afteraincc/Simple-AR/3d-model/debug/lens-2.step

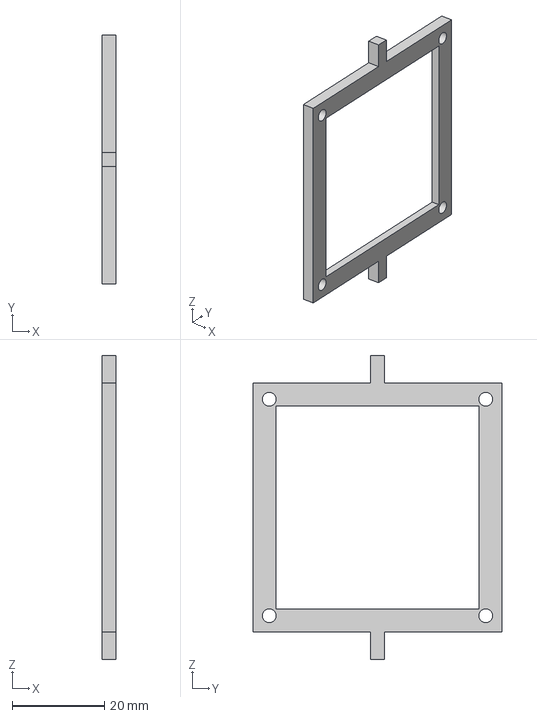
[picture p23: CAD file, 2023-01-13]
3d-model/debug/lens-2.step
3.00 x 54.0 x 66.0 mm
