afteraincc/Simple-AR/3d-model/debug/back.step

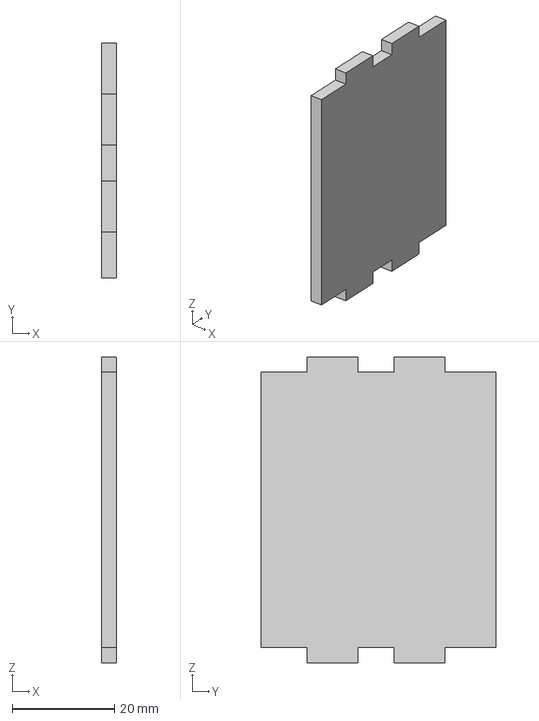
[picture p24: CAD file, 2023-01-13]
3d-model/debug/back.step
3.00 x 46.0 x 59.9 mm
