afteraincc/Simple-AR/3d-model/debug/beam-top.step

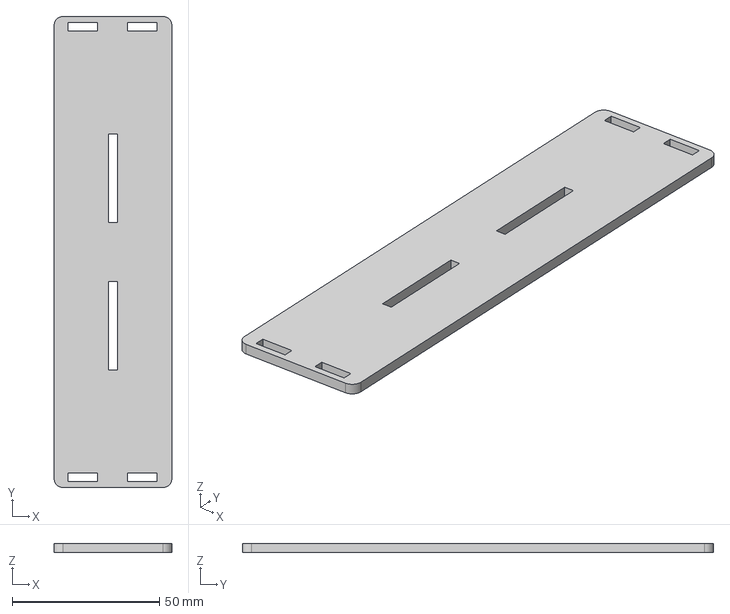
[picture p25: CAD file, 2023-01-13]
3d-model/debug/beam-top.step
40.0 x 160.0 x 3.00 mm
