afteraincc/Simple-AR/3d-model/debug/ear-bottom.step

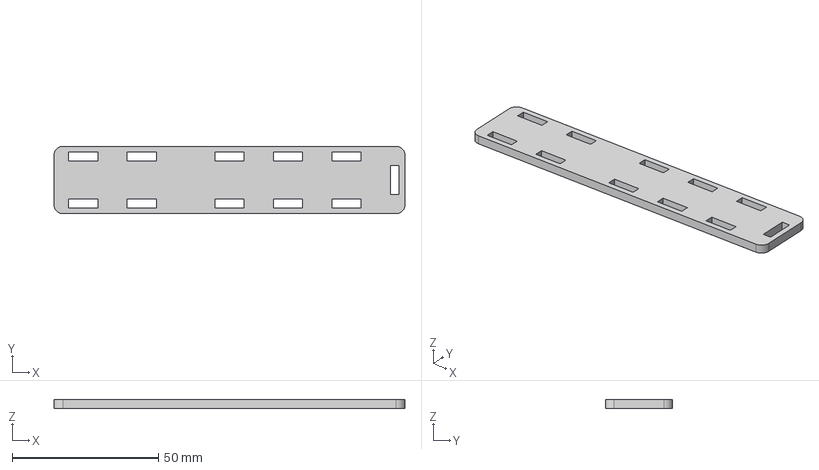
[picture p26: CAD file, 2023-01-13]
3d-model/debug/ear-bottom.step
120.0 x 23.0 x 3.00 mm
