afteraincc/Simple-AR/3d-model/debug/lens-beam.step

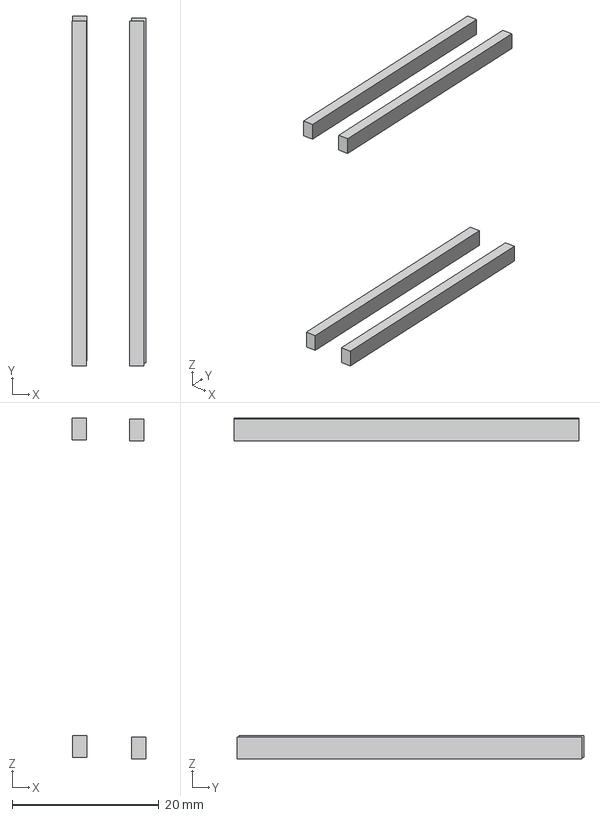
[picture p27: CAD file, 2023-01-13]
3d-model/debug/lens-beam.step
10.1 x 47.7 x 46.5 mm
lens-beam-1
lens-beam-2
lens-beam-3
lens-beam-4
