afteraincc/Simple-AR/3d-model/debug/beam-column-2.step

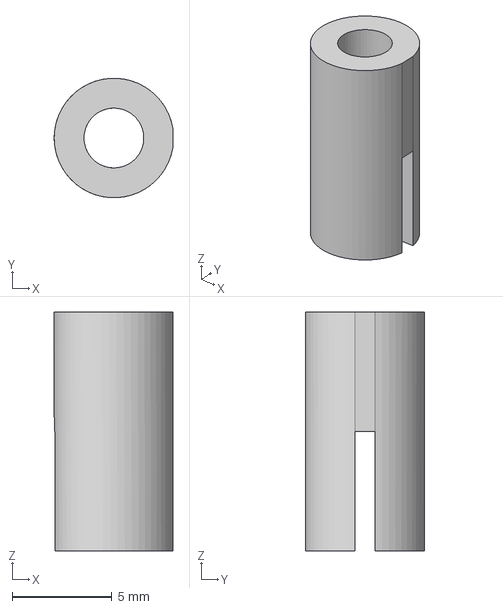
[picture p28: CAD file, 2023-01-13]
3d-model/debug/beam-column-2.step
5.96 x 6.00 x 12.0 mm
