afteraincc/Simple-AR/3d-model/debug/display-beam.step

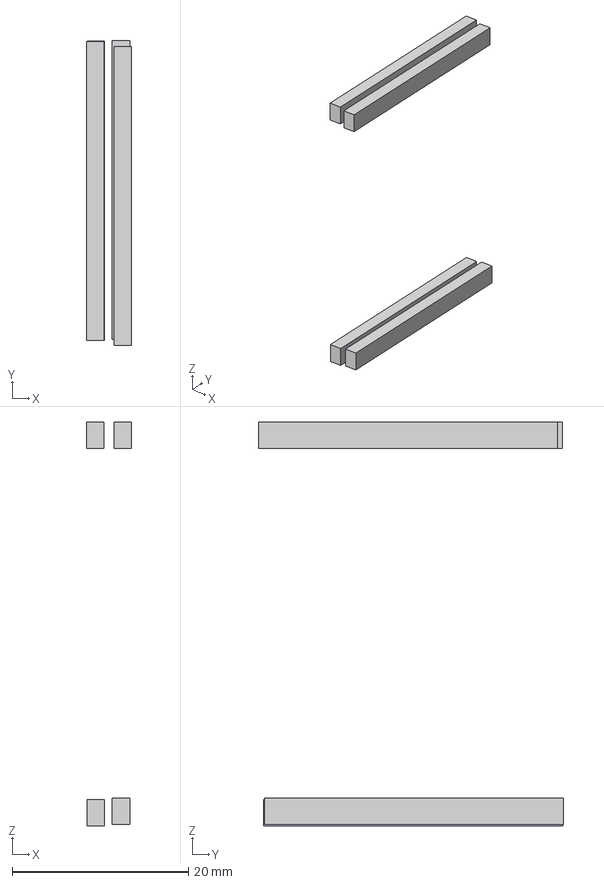
[picture p29: CAD file, 2023-01-13]
3d-model/debug/display-beam.step
5.12 x 34.7 x 45.9 mm
display-beam-1
display-beam-2
display-beam-3
display-beam-4
